JustAnEric/starbiez/circuit/starbie2.png

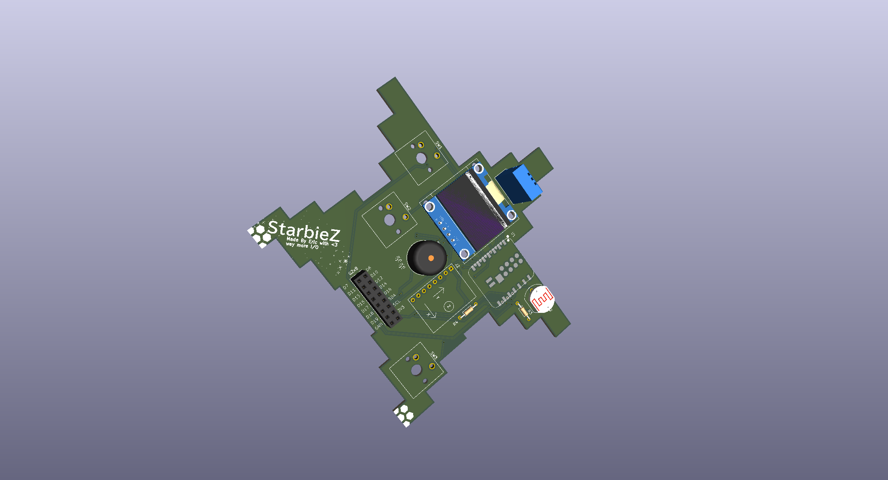
circuit/starbie2.png
