JustAnEric/starbiez/circuit/starbie3.png

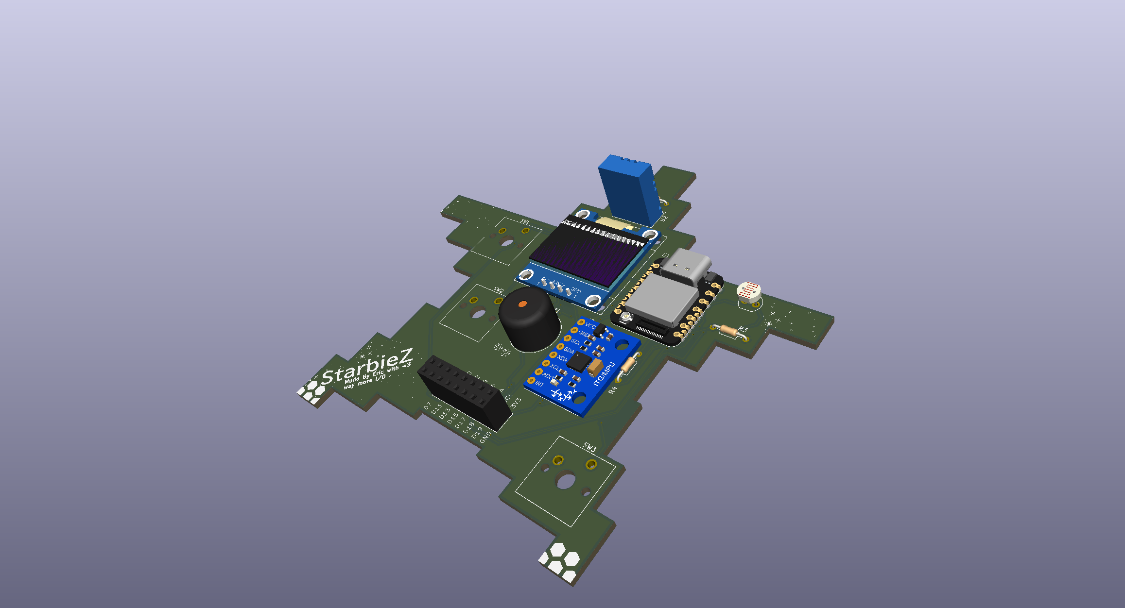
circuit/starbie3.png
