JustAnEric/starbiez/circuit/starbie4.png

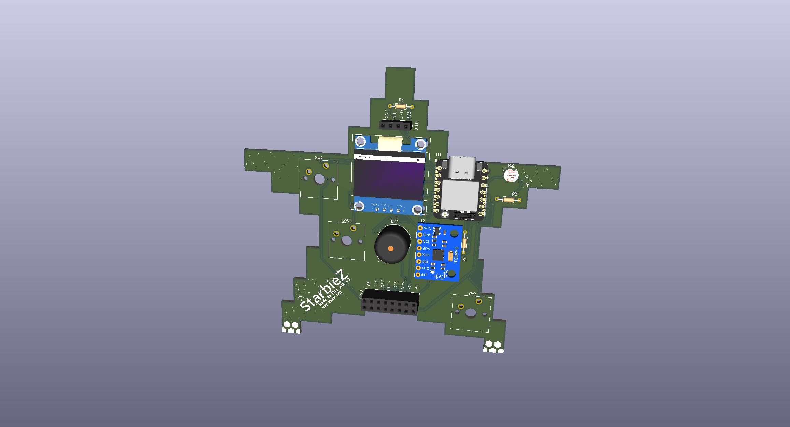
circuit/starbie4.png
