JustAnEric/starbiez/circuit/starbieshwcs2.png

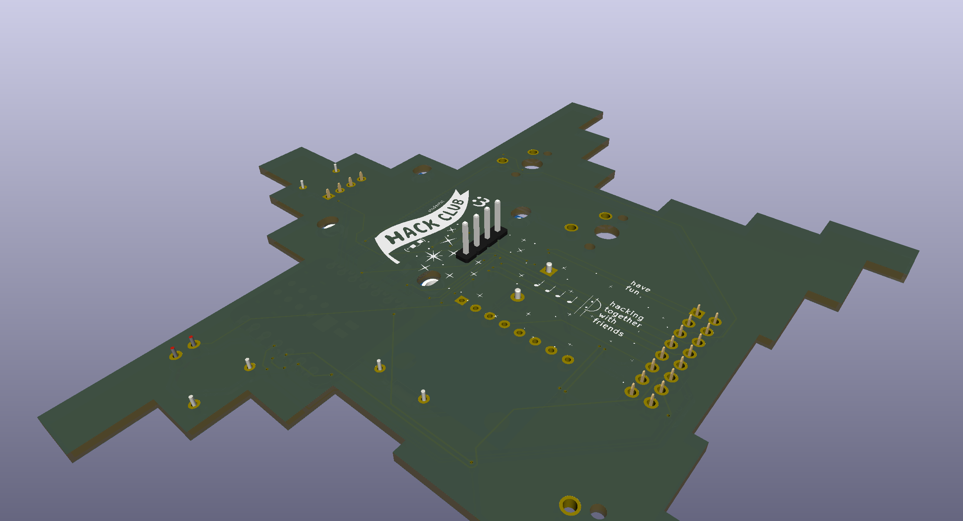
circuit/starbieshwcs2.png
