JustAnEric/starbiez/circuit/starbieshwcs3.png

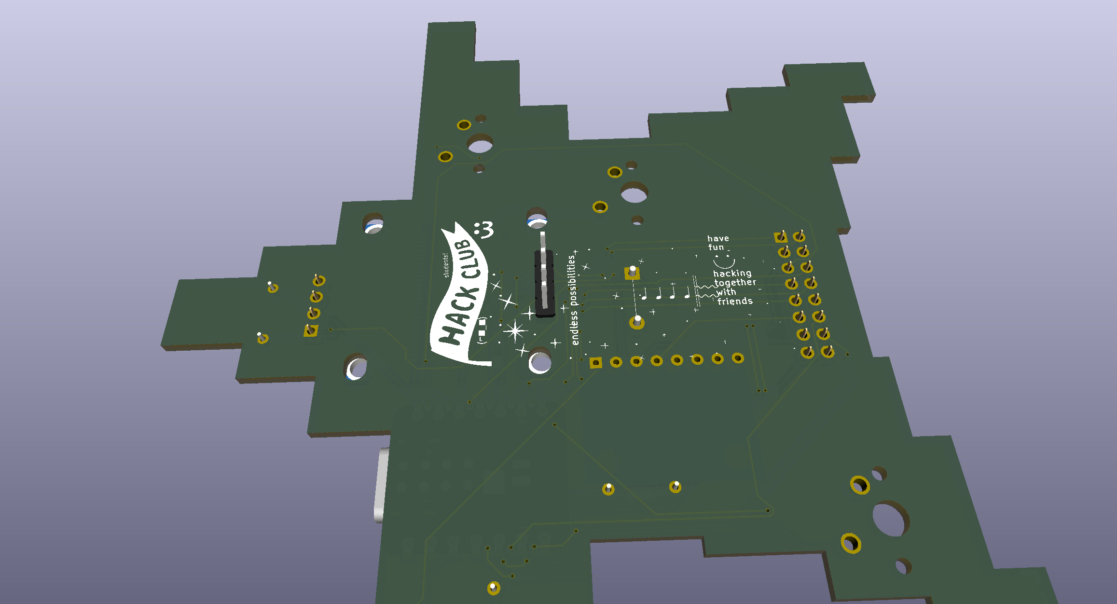
circuit/starbieshwcs3.png
