JustAnEric/starbiez/circuit/starbieshwcs3.v2.png

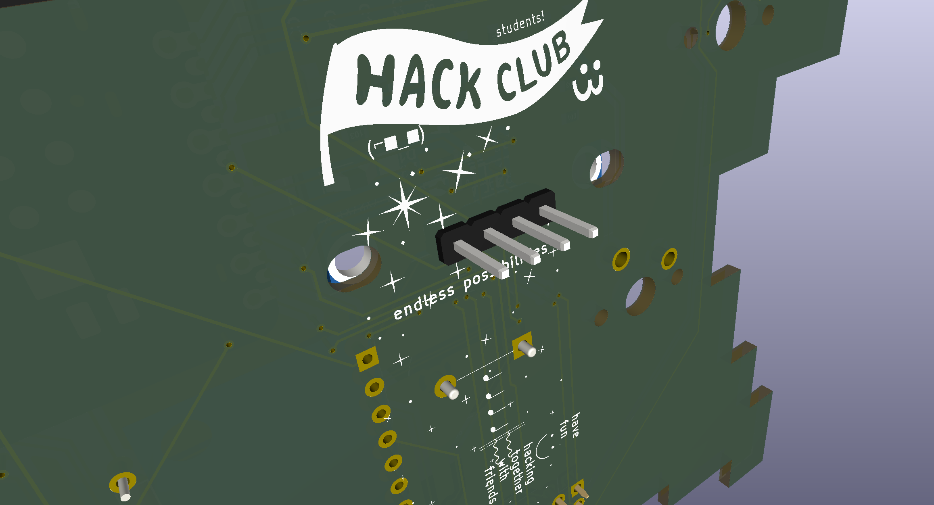
circuit/starbieshwcs3.v2.png
