JustAnEric/starbiez/circuit/starbieshwcs3.v3.png

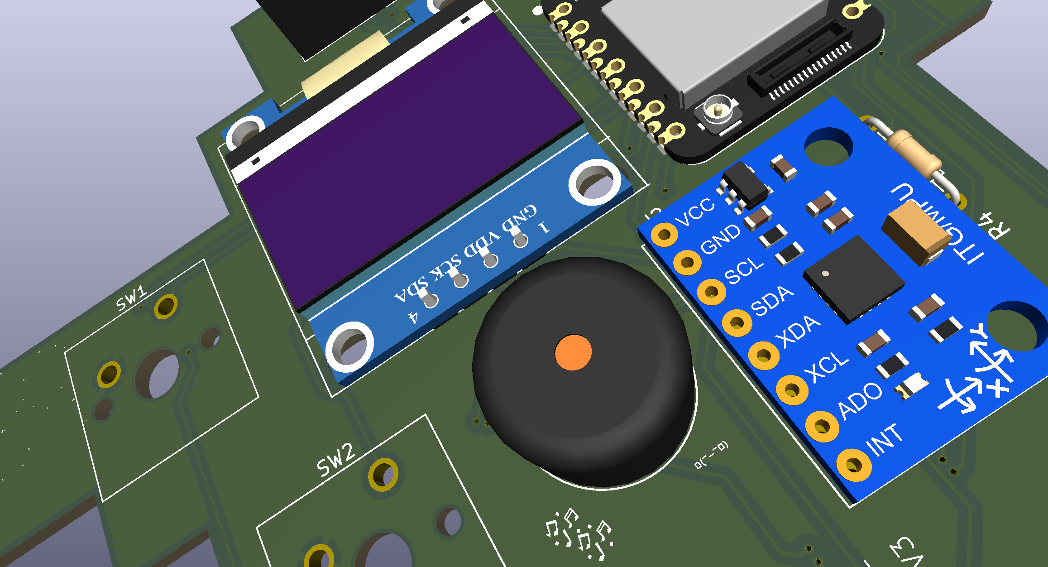
circuit/starbieshwcs3.v3.png
