JustAnEric/starbiez/circuit/starbieshwcs.png

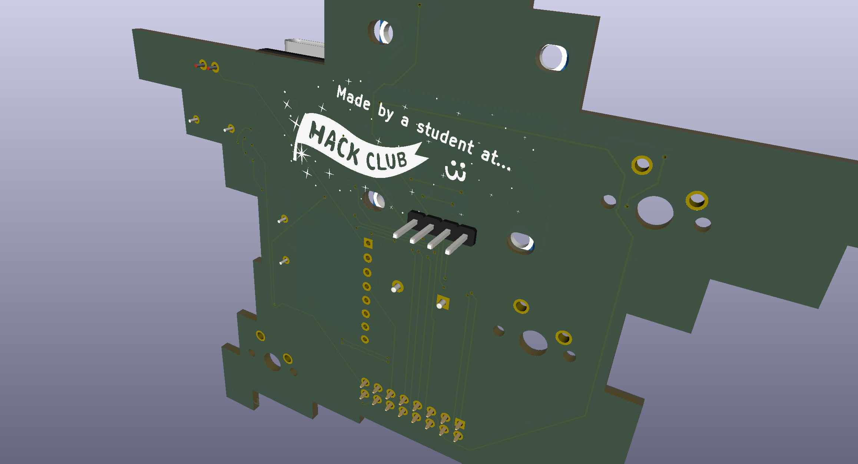
circuit/starbieshwcs.png
